claudioolmedo/risc-v/Board/Eagle Files/Brain_0.1.rv1.sch

## EAGLE design Board/Eagle Files/Brain_0.1.rv1.sch (2022-11-26)

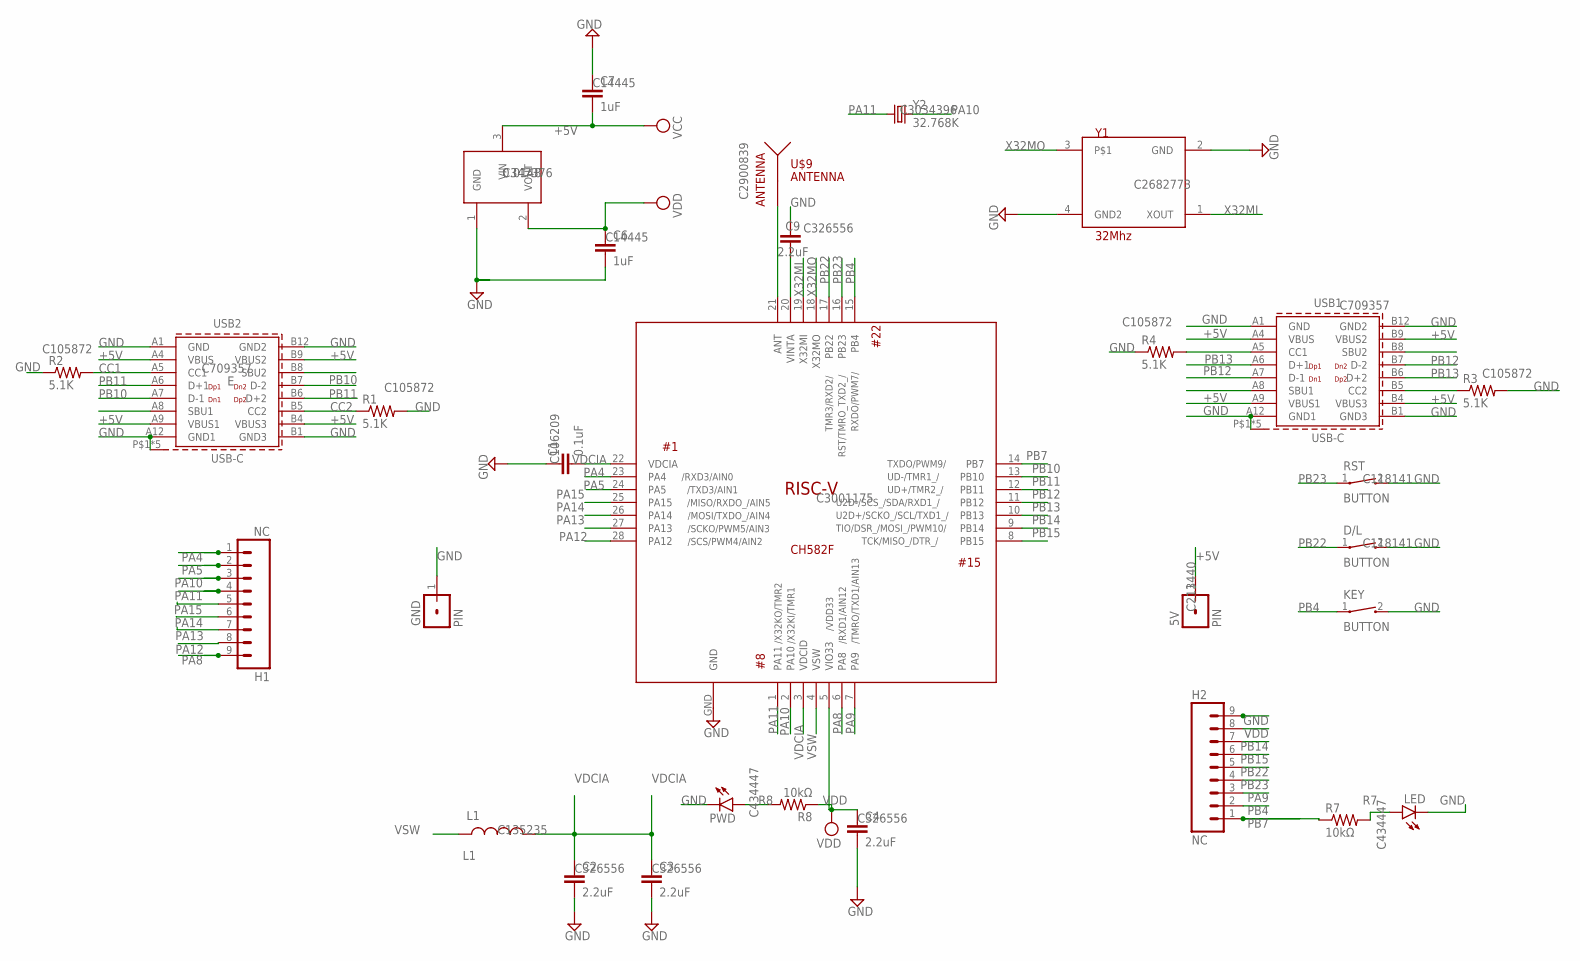
[picture p3: schematic Brain_0.1.rv1.sch]

Parts:
5V: PIN; 1X01; LCSC C213440
C1: 0.1uF; C1; LCSC C106209
C2, C3, C4, C9: 2.2uF; C1; LCSC C326556
C6, C7: 1uF; C1; LCSC C14445
D/L: BUTTON; SOD8037X250N; LCSC C118141
GND: PIN; 1X01; LCSC C213440
H1, H2: NC; 61300911821
KEY: BUTTON; SOD8037X250N; LCSC C118141
L1: L1; RESC3025X120N; LCSC C135235
LED: LED; CAPCP1005X40N; LCSC C434447
PWD: LED; CAPCP1005X40N; LCSC C434447
R1, R2, R3, R4: 5.1K; R0402; LCSC C105872
R7, R8: 10kΩ; R0402; LCSC C25744
RST: BUTTON; SOD8037X250N; LCSC C118141
U1: U1; SOT95P240X90-3N; LCSC C347376
U$8: RISC-V; QFN40P400X400X75-29T280N; LCSC C3001175
U$9: ANTENNA; CAPCP3015X50N; LCSC C2900839
USB1, USB2: 629722000214; LCSC C709357
Y1: Y1YSX211SL; OSCCC200X160X50N; LCSC C2682773
Y2: 32.768K; XTAL700X315X230N; LCSC C3034396

Connections:
+5V: 5V.1, C7.2, U1.3 (VIN), USB1.A4 (VBUS), USB1.A9 (VBUS1), USB1.B4 (VBUS3), USB1.B9 (VBUS2), USB2.A4 (VBUS), USB2.A9 (VBUS1), USB2.B4 (VBUS3), USB2.B9 (VBUS2)
CC1: R2.2, USB2.A5 (CC1)
CC2: R1.1, USB2.B5 (CC2)
GND: C1.1, C2.2, C3.2, C4.2, C6.2, C7.1, C9.1, D/L.2, GND.1, H2.9, KEY.2, LED.C, PWD.C, R1.2, R2.1, R3.2, R4.1, RST.2, U1.1 (GND), U$8.GND, USB1.A1 (GND), USB1.A12 (GND1), USB1.B1 (GND3), USB1.B12 (GND2), USB1.P$1 (SHIELD), USB2.A1 (GND), USB2.A12 (GND1), USB2.B1 (GND3), USB2.B12 (GND2), USB2.P$1 (SHIELD), Y1.2 (GND), Y1.4 (GND2)
unnamed: U$8.21 (ANT), U$9.1
unnamed: C9.2, U$8.20 (VINTA)
unnamed: R3.1, USB1.B5 (CC2)
unnamed: R4.2, USB1.A5 (CC1)
PA4: H1.1, U$8.23 (PA4)
PA5: H1.2, U$8.24 (PA5)
PA8: H1.9, U$8.6 (PA8)
PA9: H2.3, U$8.7 (PA9)
PA10: H1.3, U$8.2 (PA10), Y2.2
PA11: H1.4, U$8.1 (PA11), Y2.1
PA12: H1.8, U$8.28 (PA12)
PA13: H1.7, U$8.27 (PA13)
PA14: H1.6, U$8.26 (PA14)
PA15: H1.5, U$8.25 (PA15)
PB4: H2.2, KEY.1, U$8.15 (PB4)
PB7: H2.1, R7.1, U$8.14 (PB7)
PB10: U$8.13 (PB10), USB2.A7 (D-1), USB2.B7 (D-2)
PB11: U$8.12 (PB11), USB2.A6 (D+1), USB2.B6 (D+2)
PB12: U$8.11 (PB12), USB1.A7 (D-1), USB1.B7 (D-2)
PB13: U$8.10 (PB13), USB1.A6 (D+1), USB1.B6 (D+2)
PB14: H2.7, U$8.9 (PB14)
PB15: H2.6, U$8.8 (PB15)
PB22: D/L.1, H2.5, U$8.17 (PB22)
PB23: H2.4, RST.1, U$8.16 (PB23)
R7: LED.A, R7.2
R8: PWD.A, R8.2
VDCIA: C1.2, C2.1, C3.1, L1.2, U$8.3 (VDCID), U$8.22 (VDCIA)
VDD: C4.1, C6.1, H2.8, R8.1, U1.2 (VOUT), U$8.5 (VIO33)
VSW: L1.1, U$8.4 (VSW)
X32MI: U$8.19 (X32MI), Y1.1 (XOUT)
X32MO: U$8.18 (X32MO), Y1.3
